f4grx/sys11/docs/pics/protoboard/01_proto_top.jpg

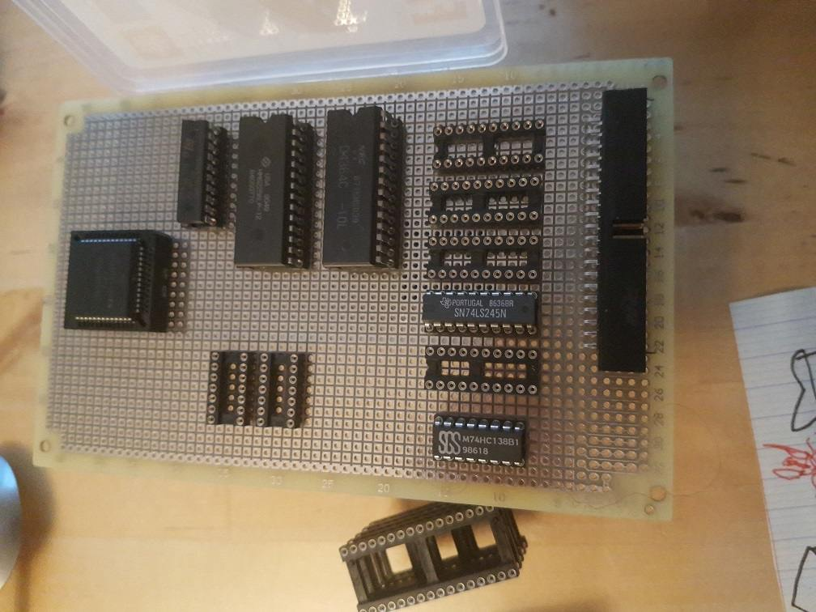
docs/pics/protoboard/01_proto_top.jpg
