f4grx/sys11/docs/pics/protoboard/06_proto_bot.jpg

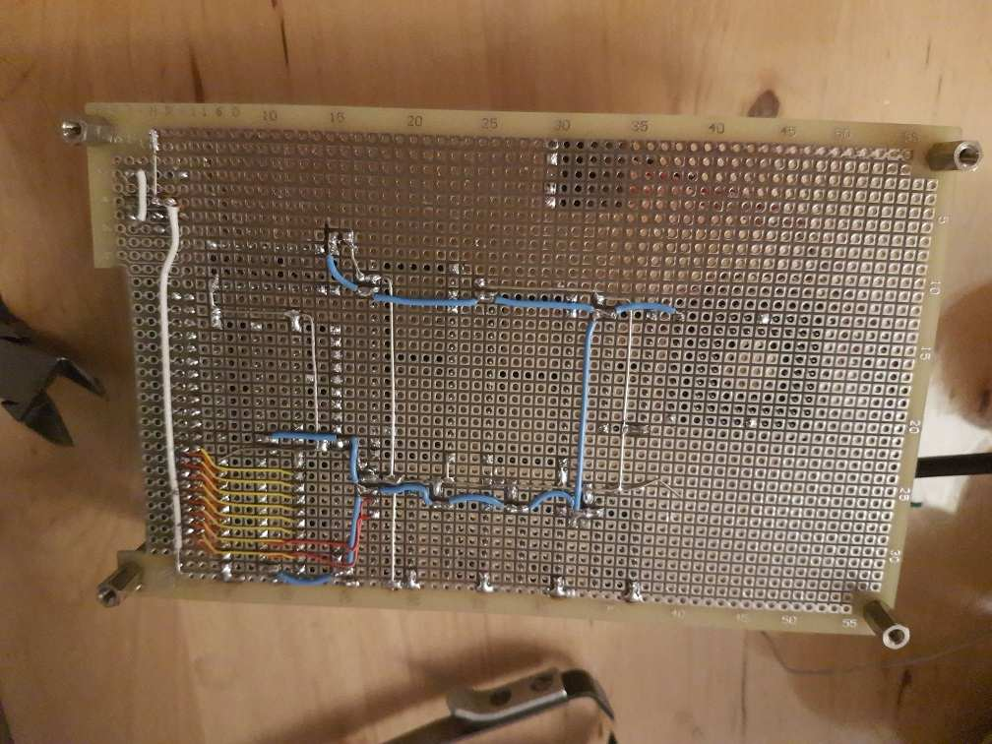
docs/pics/protoboard/06_proto_bot.jpg
