f4grx/sys11/docs/pics/protoboard/09_proto_top.jpg

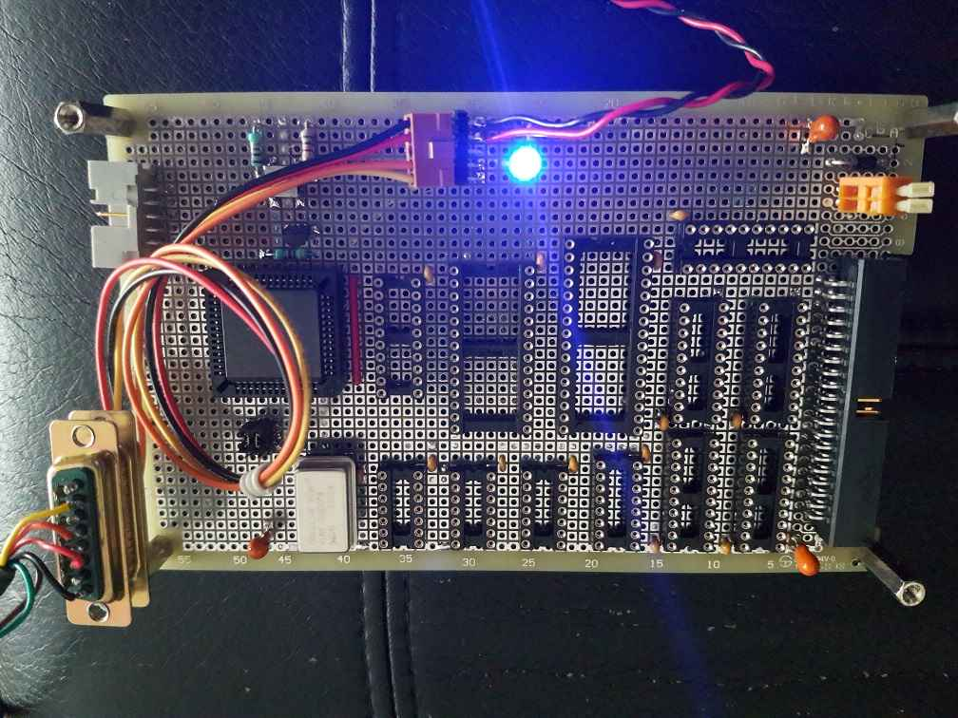
docs/pics/protoboard/09_proto_top.jpg
