f4grx/sys11/docs/pics/protoboard/12_proto_top.jpg

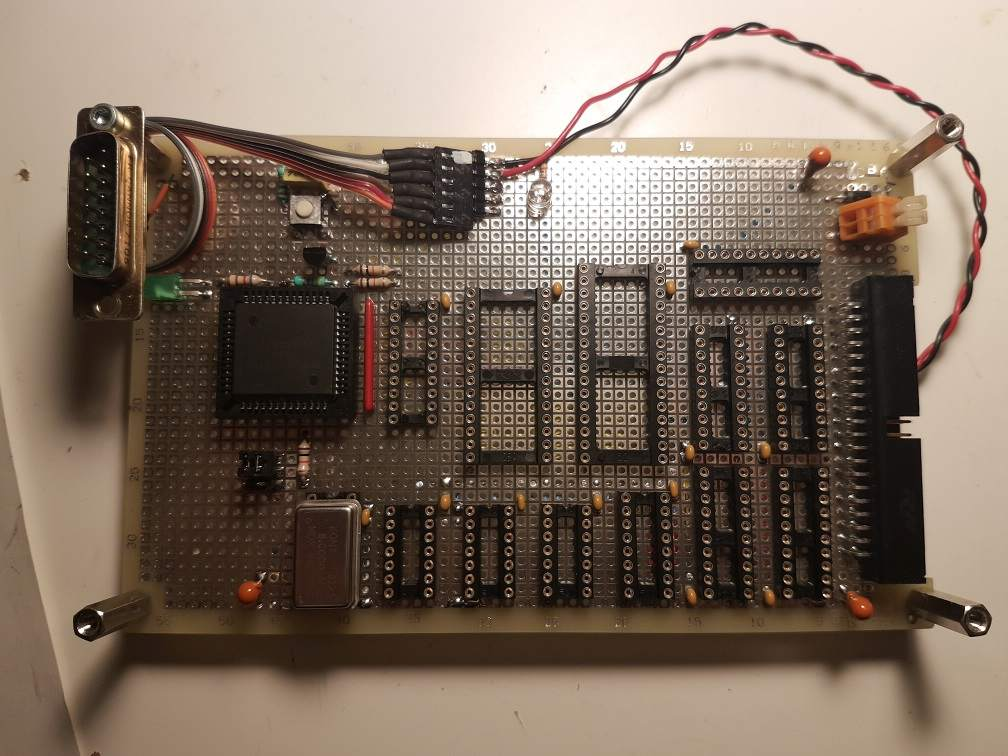
docs/pics/protoboard/12_proto_top.jpg
