f4grx/sys11/monitor/shell.asm

/* sys11 shell */
/* TODO modularize this in two calls: readline and execute,
 * so each can be reused. */

	.include "serial.inc"
	.include "stdio.inc"

	.equ SCMD_MAX, 80+1	/* Include final zero */
	.equ ARGV_MAX, 8

/*===========================================================================*/
	.section .rodata
sprompt:
	.asciz "sys11>"
son:	.asciz "ON"
soff:	.asciz "OFF"
snocom:	.asciz "???"

	.section .scommands_start
scommands:
	.asciz	"echo"
	.word	shell_echo

	.section .scommands_end
	.byte	0xFF	/* End of list */

/*===========================================================================*/
	.section .edata
scmdbuf:
	.space	SCMD_MAX /* Storage for command line */
argc:
	.byte	0
argv:
	.space	ARGV_MAX * 2

	.text

/*===========================================================================*/
	.func	shell_echo
shell_echo:
	ldaa	rlopts
	eora	#OPT_ECHO
	beq	.Lnoecho2
	ldx	#son
	bra	.Ldisp
.Lnoecho2:
	ldx	#soff
.Ldisp:
	staa	rlopts
	stx	*sp0
	jsr	serial_puts
	jsr	serial_crlf
	rts
	.endfunc

/*===========================================================================*/
/* Parse zero terminated string at address sp0.
   Store arguments in array at address sp1 (max entries in sp2.L).
   Passed string is modified and gets zero bytes to separate the args.
   Returns argc in B (D.L)
   Spaces are trimmed before and after the command line.
   Arguments can be separated by more than one space
   Quotes are not taken into account for
 */
	.func	shell_parse
	.global	shell_parse
shell_parse:

	/* Save used temps */

	ldx	*st0
	pshx
	ldx	*st1
	pshx
	clrb
	stab	*(st1+1)		/* Clear argument count */
	ldx	*sp0

	/* Skip spaces at beginning of string */

.Lprespaces:
	ldab	0,X
	cmpb	#0x20
	bne	.Lpreloop
	inx
	bra	.Lprespaces
.Lpreloop:
	stx	*st0

.Lparseloop:
	/* Store current string pointer in current arg */
	clra
	ldab	*(st1+1)	/* D now contains cur number of arguments */
	cmpb	*(sp2+1)	/* Max num of args reached ? */
	beq	.Lparsedone	/* Then we're finished */
	lsld			/* D now contains offset in argv array to store arg N */
	addd	*sp1		/* D now contains destination pointer to store arg N */
	ldx	*st0		/* This is the current char pointer */
	xgdx			/* Swap X and D because we can only store at X */
	std	0,X		/* Store pointer to arg N */

	/* Increment arg count */

	inc	*(st1+1)	/* Increment arg count */

	/* Skip all chars until next space or end of string. */

	ldx	*st0		/* This is the current char pointer */
.Lsplit:
	ldaa	0,X		/* Get command char */
	beq	.Lparsedone	/* Zero? Then finish parsing. */
	cmpa	#0x20		/* If its a space, */
	beq	.Lfoundspace	/* Then current arg is complete */
	inx			/* Prepare for next char */
	bra	.Lsplit		/* Try again (next char) */

	/* Split the argument at this first space */

.Lfoundspace:
	clra			/* Put an end of arg/str marker */
	staa	0,X		/* Where we had a space */

	/* Check for more spaces after this one*/

.Lspaceagain:
	inx			/* Point to char right after space */
	ldaa	0,X		/* Get this following char */
	cmpa	#0x20		/* Still a space? */
	beq	.Lspaceagain	/* Then skip. */

	stx	*st0		/* X is now a pointer to the next non-space char */
	ldaa	0,X		/* reached end of string */
	beq	.Lparsedone	/* finished */
	bra	.Lparseloop	/* This next char is not the start of a new arg */
.Lparsedone:
	clra
	ldab	*(st1+1)

	/* Restore temporaries to their state before the call */

	pulx
	stx	*st1
	pulx
	stx	*st0
	rts
	.endfunc

/*===========================================================================*/
/* Shell execute, using globals argc and argv positioned after shell_parse.
 * Find the function in argv[0] and execute it.
 */
	.func	shell_exec
	.global	shell_exec
shell_exec:

	/* Initialize browsing of command list */

	ldx	#scommands	/* Command List head */
	stx	*sp0		/* Init loop with pointer to first command */

.Lnextcmd:

	/* Prepare to skip name of current command */

	jsr	strlen
	addd	*sp0
	xgdx
	inx			/* Skip final zero */
	stx	st0		/* Store in temp for reuse when skipping to next cmd */

	/* Compare argv[0] with command being pointed at */

	ldx	argv
	stx	*sp1		/* Command name in sp1 */
	jsr	strcmp		/* Compare with buffered command */
	beq	.Lfound

	/* Typed command is not the current command. Try next. */

	ldx	*st0
	inx
	inx			/* skip function pointer */
	stx	*sp0		/* X now points to name of next command */
	ldaa	0,X
	cmpa	#0xFF
	beq	.Lnocommand	/* Reached end of command list, nothing found, acq next user cmd */
	bra	.Lnextcmd	/* Compare cmd buffer with next command in list */

.Lnocommand:

	/* All commands were examined and argv[0] is not in them. Return error. */

	ldab	#1
	bra	.Lfinish

.Lfound:

	/* Execute the command with a jump. Params sp0 and sp1 are still valid. */

	ldx	*st0	/* st0 stored the pointer right after the cmd name */
	ldx	0,X	/* Get address stored right after the name */
	jsr	0,X	/* Jump at this address */
	clrb	
.Lfinish:
	clra
	rts
	.endfunc

/*===========================================================================*/
	.func	app_main
	.global app_main
app_main:
	ldaa	#OPT_ECHO		/* Default to echo ON */
	staa	rlopts

.Lcmdloop:
	/* ==================== */
	/* Display main prompt */
	/* ==================== */

	ldx	#sprompt
	stx	*sp0
	jsr	serial_puts

	/* ==================== */
	/* Acquire a line of text */
	/* ==================== */

	ldx	#scmdbuf
	stx	*sp0
	ldx	#(SCMD_MAX)	/* scmdbuf has additional byte to store 80 chars + final zero */
	stx	*sp1
	jsr	readline
	jsr	serial_crlf	/* Skip current line */

.if 0
	/* Test display for readline */
	ldx	#scmdbuf
	stx	*sp0
	jsr	serial_puts
	jsr	serial_crlf	/* Skip current line */
	bra	.Lcmdloop
.endif

	/* ==================== */
	/* Split command into arguments */
	/* ==================== */

	ldx	#argv
	stx	*sp1
	clra
	ldab	#ARGV_MAX
	std	*sp2
	jsr	shell_parse
	stab	argc

.if 0
	/* Debug: display arg count */
	clra
	ldab	argc
	std	*sp0
	jsr	serial_putdec
	jsr	serial_crlf
	clra
	clrb
	std	*st0
.Lnextarg:
	std	*sp0
	jsr	serial_putdec
	.section .rodata
arrow:	.asciz	" -> "
	.text
	ldx	#arrow
	stx	*sp0
	jsr	serial_puts
	ldd	*st0
	lsld
	ldx	#argv
	abx
	ldd	0,X
	std	*sp0
	jsr	serial_puts
	jsr	serial_crlf
	/* set for next arg */
	ldd	*st0
	incb
	std	*st0
	cmpb	argc
	blo	.Lnextarg
	bra	.Lcmdloop
.endif

	/* ==================== */
	/* Execute command */
	/* ==================== */
	std	*sp0
	ldx	#argv
	stx	*sp1
	jsr	shell_exec
	tstb	
	beq	.Lcmdloop	/* Command success: wait next command */

	/* Command error: Display error message */

	ldx	#snocom
	stx	*sp0
	jsr	serial_puts
	jsr	serial_crlf
	bra	.Lcmdloop

	rts
	.endfunc
