f4grx/sys11/monitor/mm.asm

/* Memory management routines */


	.include "softregs.inc"

	.extern	HEAPSTART
	.extern	HEAPEND

	.data
head:	.word	0 /* Pointer to the first free zone */

	.text

/* Initialize the heap.
 * We define a single free space starting at address RAMSTART
 * Parameters: None
 * Return value: None
 */
	.func	mm_init
	.global	mm_init
mm_init:
	ldx	#HEAPSTART
	ldd	#HEAPEND
	subd	#HEAPSTART
	subd	#2
	std	0,X
	ldd	#0xffff
	std	2,X		/* This is the pointer to next (none) */
	stx	head		/* Initialize head of free zone list */
	rts
	.endfunc

/* Allocate a memory zone.
 * Parameters:
 *   sp0 requested_size
 * Return value:
 *   D   Pointer to memory zone, possibly NULL if failed to alloc
 */
	.func	mm_alloc
	.global mm_alloc
mm_alloc:
	/* Browse all zones in the free list.
	 * We need one that is larger than the requested size
	 */
	ldx	head
	stx	*st3	/* *st3 <- adr */
.Lagain:
	ldx	*st3	/* X <- adr */
	ldd	0,X	/* X <- adr.siz */
	cpd	*sp0	/* Compare adr.siz and size */
	blo	.Lnext	/* Current free block smaller than request? try next */
	/* At this point we have a zone that is big enough for allocation */
	beq	.Lalloc	/* Zone has the correct size */
	/* Zone is larger than requested, we have to do a split */	
.Lsplit:
	ldd	*sp0	/* D <- size */
	addd	#2	/* D <- size + 2 */
	addd	*st3	/* D <- size + 2 + adr == nxtadr */
	std	*st1	/* *st1 <- nxtadr */

	ldx	*st3	/* X <- adr */
	ldd	0,X	/* D <- PEEK(adr+SIZE) */
	subd	#2	/* D <- PEEK(adr+SIZE) - 2 */
	subd	*sp0	/* D <- PEEK(adr+SIZE) - 2 - size == tmp */
	ldx	*st1	/* X <- nxtadr */
	std	0,X	/* POKE(nxtadr+SIZE, tmp)*/

	ldx	*st3	/* X <- adr */
	ldd	2,X	/* D <- PEEK(adr+NEXT) == tmp */
	ldx	*st1	/* X <- nxtadr */
	std	2,X	/* POKE(nxtadr+NEXT, tmp) */

	ldx	*st3	/* X contain adr */
	ldd	*st1	/* D <- nxtadr */
	std	2,X	/* POKE adr+NEXT, nxtadr */
	ldd	*sp0	/* D <- size */
	std	0,X	/* POKE adr+SIZE, size */

	/* now the current free zone @*sp3 has the correct size */

.Lalloc: /* at this point X contains st3 */
	/* Set the mem fields to allocate this zone */
	ldd	*st1 		/* Get next zone pointer */
	cpx	head		/* is cur zone (alloced) the head of free list? */
	bne	.Lremlist	/* no: remove cur block from free list */
	/* yes: so the head is the zone after the allocated block */
	std	head		/* Update head */
	bra	.Lretblock
.Lremlist:
	ldy	*st0		/* Y <- prev_adr (avoid overwriting st3 in X) */
	std	2,Y		/* POKE prevadr+NEXT, nxtadr (skip curblock in freelist) */
.Lretblock:
	inx			/* X still has *sp3(adr), skip size */
	inx			/* skip size */
	xgdx			/* put in D, X gets garbage */
	bra	.Lend		/* We're done! */

.Lnext:	/* Setup pointers to look at next block */
	stx	*st0	/* st0 : prev_adr (potential use at next round) */
	ldx	2,X	/* Get curzone->next */
	cpx	#0xffff	/* Is next the end of the list? */
	beq	.Ldone	/* Yes, alloc was not possible, were done */
	stx	*st3	/* now current zone is next zone */
	bra	.Lagain	/* Try to fit the request in the next zone */
.Ldone:
	/* We reached the end of free zones without finding a big enough one */
	/* We have to fail the allocation by returning NULL */
	clra	/* DL <- 0 */
	clrb	/* DH <- 0 */
.Lend:
	rts
	.endfunc

/* Release a memory zone.
 * After this call the pointed memory zone is considered free for allocation.
 * Parameters:
 *   sp0 pointer_to_zone
 * Return value: None
 */
	.func	mm_free
	.global mm_free
mm_free:
	ldx	*sp0	/* X <- pointer to user data to free */
	dex		/* Get pointer to zone */
	dex		/* X <- adr */
	stx	*sp0	/* sp0 <- adr */
	cpx	head	/* Compare adr with head */
	bhs	.Lbrowse
	/* adr is < head, replace head */
	ldd	head	/* D <- head */
	std	2,X	/* POKE(adr+NEXT, head) */
	stx	head	/* head <- adr */
	bra	.Lcoalesce

	/* Browse free list to find insertion point */
.Lbrowse:
	ldx	head	/* X == cur <- head */
.Lbrowsenext:
	cpx	#0xFFFF	/* Check end of list */
	beq	.Leol
	ldd	2,X	/* D == nxt <- PEEK(cur+NEXT) */
	cpd	*sp0
	bhi	.Leol	/* break if next > adr, D has nxt, X has cur */
	xgdx		/* X == cur <-> D == nxt : cur = nxt*/
	bra	.Lbrowsenext
.Leol:
	/* Insert into free list */
	std	2,x	/* POKE(cur+NEXT, nxt) */
	xgdx		/* D <- cur */
	ldx	*sp0	/* X <- adr */
	std	2,x	/* POKE(adr+NEXT, cur) */

	/* Coalesce - merge block if current block finishes right before next block (cur+size+2==next) */
.Lcoalesce:
	ldx	head	/* X == cur <- head */
.Lcoalloop:
	cpx	#0xFFFF	/* end of list reached? */
	beq	.Lcoaldone
	stx	*st2	/* st2 <- cur (has to be saved for use later in block merge) */
	ldd	2,X
	std	*st1	/*st1 == D <- nxt == PEEK(cur+NEXT) */
	ldd	0,X
	std	*st0	/*st0 == D <- siz == PEEK(cur+SIZE) */
	inx
	inx		/* Double inc X saves one byte wrt addd #0x0002 */
	xgdx		/* D <- cur + 2 */
	addd	*st0	/* D <- cur + 2 + siz */
	cpd	*st1	/* Compare with next */
	bne	.Lcoalnext
.Lcoaldo:
	/* free blocks adr and nxt are adjacent, can be merged */
	ldx	*st1	/* X <- nxt */
	ldd	0,X	/* D <- PEEK(nxt+SIZE) */
	addd	#2	/* D <- PEEK(nxt+SIZE) + 2 */
	addd	*st0	/* D <- siz + nxtsiz + 2 */
	ldx	*st2	/* X <- cur */
	std	0,X	/* POKE(cur+SIZE, D) */
	ldy	*st1	/* Y <- nxt */
	ldd	2,Y	/* D == nxt = PEEK(nxt+NEXT) */
	std	2,X	/* POKE(cur+NEXT, nxt) */
	bra	.Lcoalesce	/* Try again */
.Lcoalnext:
	/* These blocks are not adjacent, replace cur by next and try again for next pair */
	ldx	*st1
	bra	.Lcoalloop
.Lcoaldone:
	rts
	.endfunc
