f4grx/sys11/masm/as11.c

#include <stdio.h>
#include "as.h"
#include "table11.h"
#include "as.c"
#include "do11.c"
#include "pseudo.c"
#include "eval.c"
#include "symtab.c"
#include "util.c"
#include "ffwd.c"
#include "output.c"
